MartinStokroos/Philips_MFB_544_Visaton_modification/figures/544_capstand.png

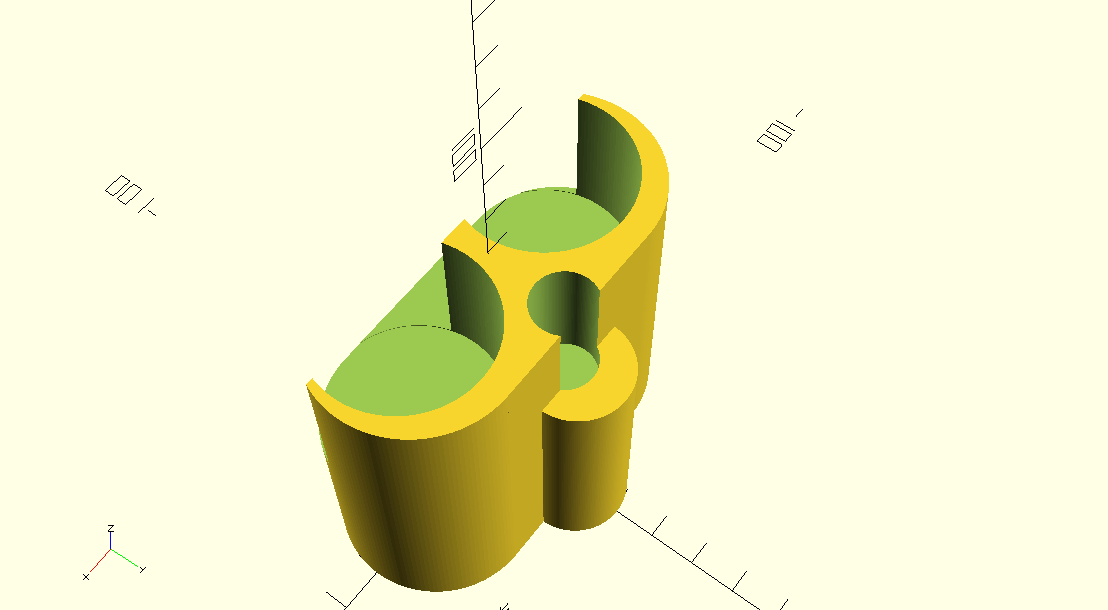
figures/544_capstand.png
